AngelDCS23/Atenea/hardware/schematics/Nevermore-1/Nevermore-1.kicad_sch

## KiCad design hardware/schematics/Nevermore-1/Nevermore-1.kicad_sch (2026-07-23, an earlier design)

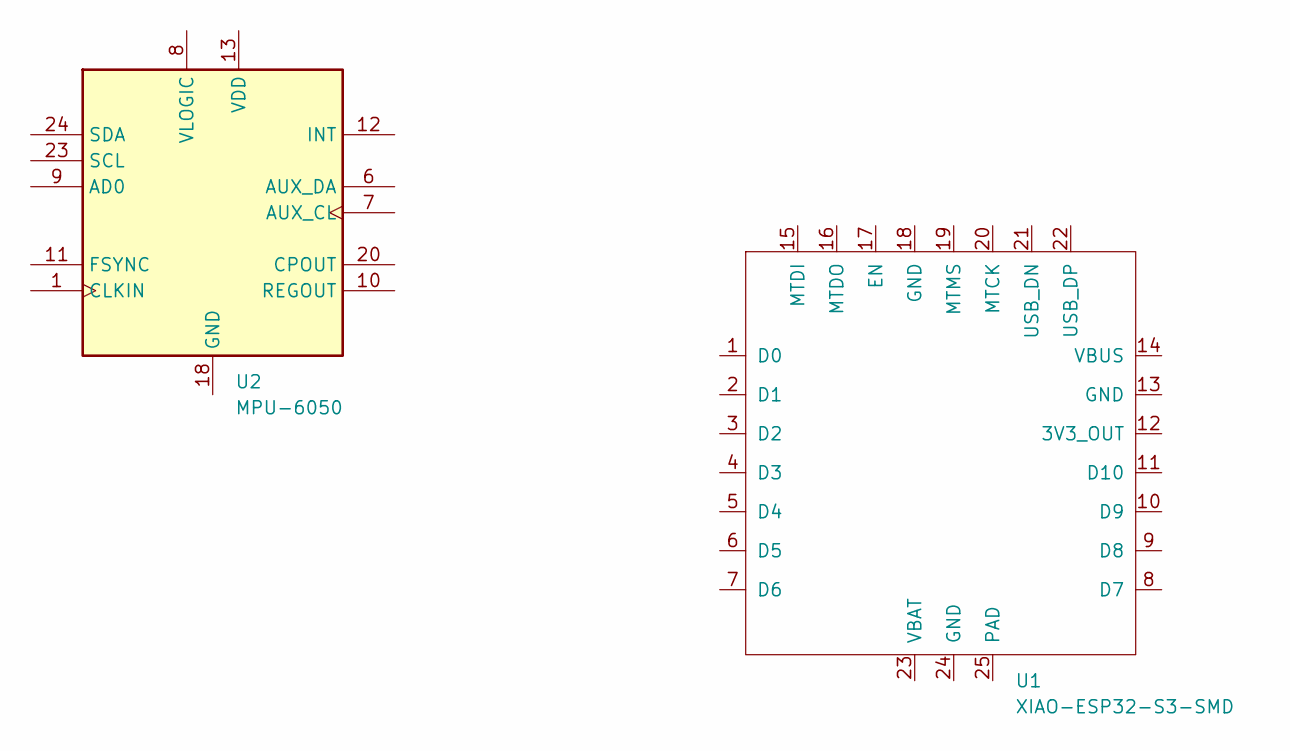
[picture p3: schematic Nevermore-1.kicad_sch]

Parts:
U1: XIAO-ESP32-S3-SMD
U2: MPU-6050; InvenSense_QFN-24_4x4mm_P0.5mm
